cewald/rpi-pico-onair-bulb/src/server.py

from lib.microdot import Microdot
from src.config import get_config
from src.display import display
from src.led import led
from lib.url_decode import url_decode

print("Init server")

app = Microdot()
config = get_config()


async def start_server(debug=True):
    port = config["port"]
    await app.start_server(port=port, debug=debug)


def returnResponse(success=True):
    return {"success": True, "state": led.value()}


@app.get("/")
async def index(request):
    return returnResponse()


@app.get("/on")
@app.get("/on/")
async def on(request):
    led.on()
    display.show_image()
    return returnResponse()


@app.get("/on/<text>")
@app.get("/on/<text>/")
async def on_with_text(request, text):
    led.on()
    display.show_text(text=text)
    return returnResponse()


@app.get("/off")
@app.get("/off/")
async def off(request):
    led.off()
    display.clear()
    return returnResponse()


@app.get("/toggle")
@app.get("/toggle/")
async def toggle(request):
    led.toggle()

    if led.value() == 0:
        display.clear()
    else:
        display.show_image()

    return returnResponse()


@app.get("/toggle/<text>")
@app.get("/toggle/<text>/")
async def toggle_with_text(request, text):
    text_change = url_decode(text) != display.text

    if led.value() == 1 and not text_change:
        display.clear()
        led.off()
    elif text_change:
        display.show_text(text=text)
        led.on()

    return returnResponse()


@app.get("/brightness")
@app.get("/brightness/")
async def brightness(request):
    display.brightness()
    return {"success": True, "state": display.current_brightness}


@app.get("/brightness/<int:value>")
@app.get("/brightness/<int:value>/")
async def brightness_with_value(request, value):
    display.brightness(value)
    return {"success": True, "state": display.current_brightness}
