cewald/rpi-pico-onair-bulb/src/image.py

image_one = bytearray(
    [
        0b00111001,
        0b10011000,
        0b00111001,
        0b10111100,
        0b01111101,
        0b11011000,
        0b00111001,
        0b10111110,
        0b01101101,
        0b11011000,
        0b01101101,
        0b10110110,
        0b01101101,
        0b11111000,
        0b01101101,
        0b10110110,
        0b01101101,
        0b11111000,
        0b01111101,
        0b10111100,
        0b01101101,
        0b10111000,
        0b01111101,
        0b10111100,
        0b01111101,
        0b10111000,
        0b01101101,
        0b10110110,
        0b00111001,
        0b10011000,
        0b01101101,
        0b10110110,
    ]
)

image_zero = bytearray(
    [
        0b00111001,
        0b10011000,
        0b00111001,
        0b10111100,
        0b01111101,
        0b11011000,
        0b00111001,
        0b10111110,
        0b01101101,
        0b11011000,
        0b01101101,
        0b10110110,
        0b01101101,
        0b11111011,
        0b01101101,
        0b10110110,
        0b01101101,
        0b11111011,
        0b01111101,
        0b10111100,
        0b01101101,
        0b10111000,
        0b01111101,
        0b10111100,
        0b01111101,
        0b10111000,
        0b01101101,
        0b10110110,
        0b00111001,
        0b10011000,
        0b01101101,
        0b10110110,
    ]
)
